fchorney/StepManiaX-LED-Arrows/3D Prints/Models/STL/Arrow Top Tail for 3 Piece.stl

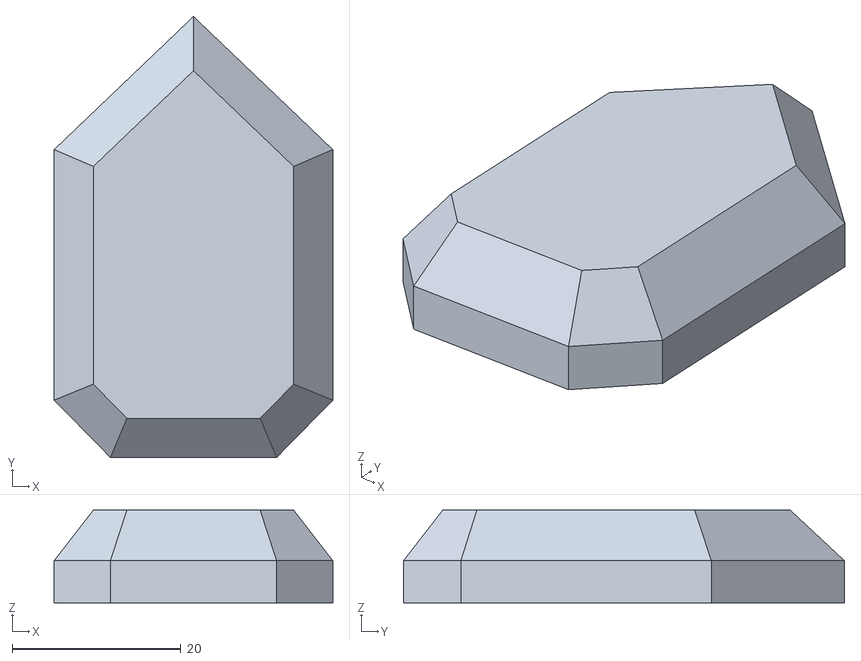
[picture p19: CAD file, 2024-01-25]
3D Prints/Models/STL/Arrow Top Tail for 3 Piece.stl
33.0 x 52.3 x 11.0
