fchorney/StepManiaX-LED-Arrows/3D Prints/Models/STL/Center Insert Middle.stl

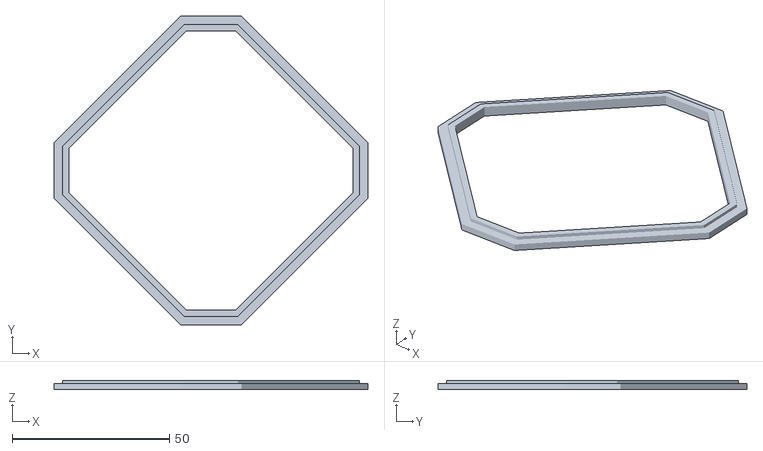
[picture p20: CAD file, 2024-01-25]
3D Prints/Models/STL/Center Insert Middle.stl
99.8 x 98.2 x 3.00
