fchorney/StepManiaX-LED-Arrows/3D Prints/Models/STL/Arrow Top Body for 3 Piece.stl

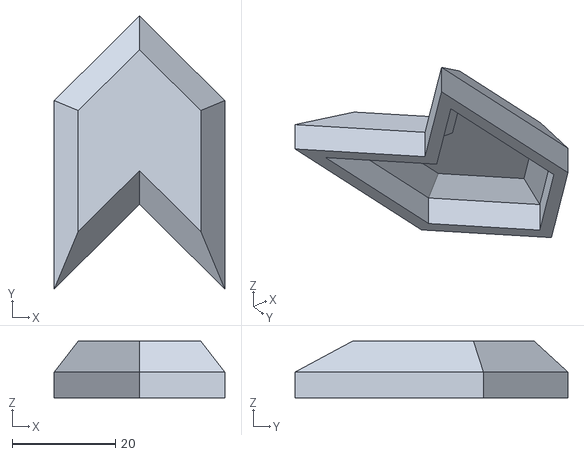
[picture p21: CAD file, 2024-01-25]
3D Prints/Models/STL/Arrow Top Body for 3 Piece.stl
33.0 x 52.9 x 11.0
