fchorney/StepManiaX-LED-Arrows/3D Prints/Models/STL/Center Top Outer.stl

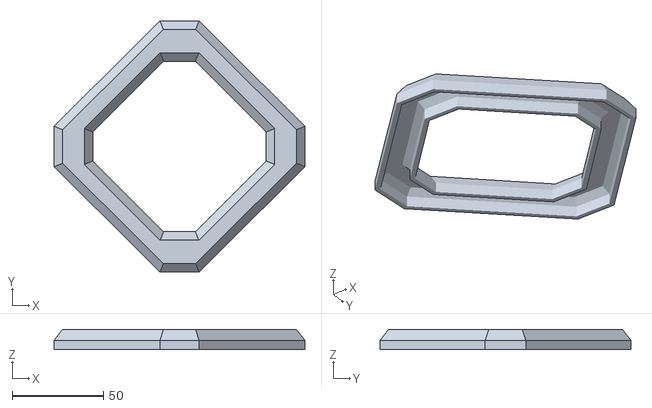
[picture p22: CAD file, 2024-01-25]
3D Prints/Models/STL/Center Top Outer.stl
137.6 x 137.6 x 11.0
