fchorney/StepManiaX-LED-Arrows/3D Prints/Models/STL/Back Plate Connector.stl

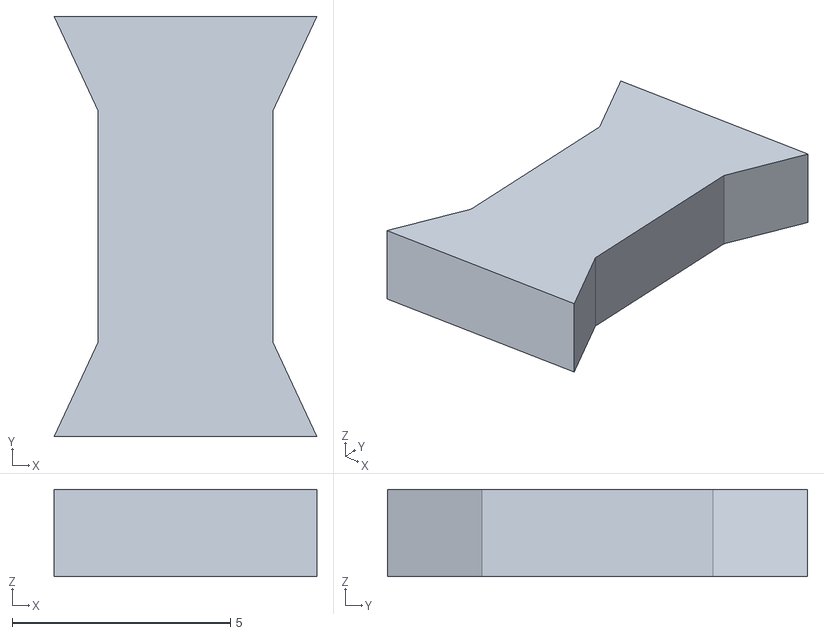
[picture p23: CAD file, 2024-01-25]
3D Prints/Models/STL/Back Plate Connector.stl
6.02 x 9.63 x 2.00
